konk22/3Def_Voron_2.4r2/images/kiauh_2.png

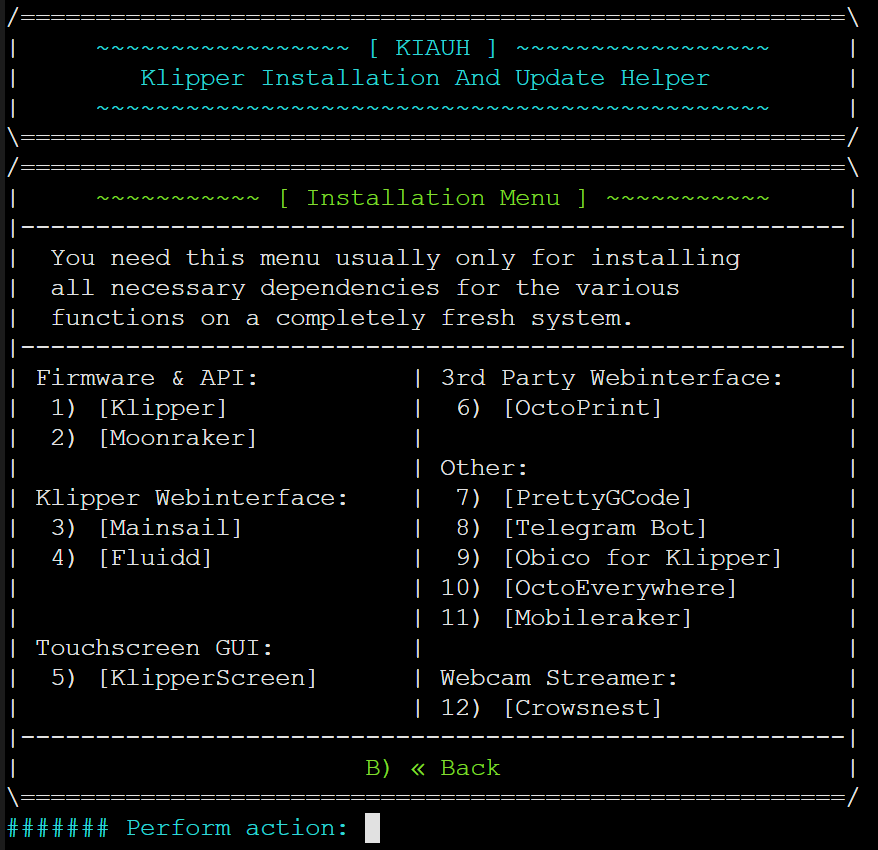
images/kiauh_2.png
