konk22/3Def_Voron_2.4r2/klipper/config/klicky/klicky-quad-gantry-level.cfg

###################
# 4Z выравнивание стола
[gcode_macro QUAD_GANTRY_LEVEL]
rename_existing: _QUAD_GANTRY_LEVEL
description: Conform a moving, twistable gantry to the shape of a stationary bed with klicky automount
gcode:
    {% set V = printer["gcode_macro _User_Variables"].verbose %}
    {% if V %}
        { action_respond_info("QG Level") }
    {% endif %}

    _CheckProbe action=query
	G90
    Attach_Probe
    _KLICKY_STATUS_LEVELING

    _QUAD_GANTRY_LEVEL {% for p in params
            %}{'%s=%s ' % (p, params[p])}{%
            endfor %}
    Dock_Probe
