konk22/3Def_Voron_2.4r2/klipper/config/adxl345.cfg

#ADXL345 Акселерометр
[adxl345]
cs_pin: sb2040:gpio1
spi_software_sclk_pin: sb2040:gpio0
spi_software_mosi_pin: sb2040:gpio3
spi_software_miso_pin: sb2040:gpio2
#axes_map: x,y,z

[resonance_tester]
accel_chip: adxl345
probe_points:
   150,150,20  # Рекомендуется настроить это место как середину нагреваемого стола 300 Настроить размер как 150,150,10
 
[gcode_macro adxl_test]
gcode:
      ACCELEROMETER_QUERY
   
[gcode_macro adxl_calibrate]
gcode:
      G28
      G1 X150 Y150 Z20 F7800   # Рекомендуется настроить это место как середину нагреваемого стола 300 Настроить размер как 150,150,10
      SET_VELOCITY_LIMIT ACCEL=16000
      SET_VELOCITY_LIMIT ACCEL_TO_DECEL=16000
      SET_INPUT_SHAPER SHAPER_FREQ_X=0 SHAPER_FREQ_Y=0
	  #M109 S100
      #M106 S128
      SHAPER_CALIBRATE
	  SAVE_CONFIG
