konk22/3Def_Voron_2.4r2/klipper/config/klicky/klicky-bed-mesh-calibrate.cfg

###################
#  Выравнивание стола
[gcode_macro BED_MESH_CALIBRATE]
rename_existing: _BED_MESH_CALIBRATE
description: Perform Mesh Bed Leveling with klicky automount
gcode:
    {% set V = printer["gcode_macro _User_Variables"].verbose %}
    {% if V %}
        { action_respond_info("Bed Mesh Calibrate") }
    {% endif %}

    _CheckProbe action=query
	G90
    Attach_Probe
    _KLICKY_STATUS_MESHING

    _BED_MESH_CALIBRATE {% for p in params
           %}{'%s=%s ' % (p, params[p])}{%
          endfor %}

    Dock_Probe
